FoamyGuy/3D-Printed-ESP8266-Remote/album_pics/2_part_design_assembled.png

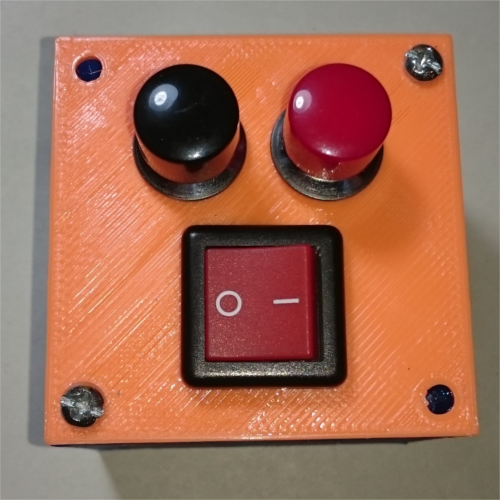
album_pics/2_part_design_assembled.png
