FoamyGuy/3D-Printed-ESP8266-Remote/album_pics/battery_brain_installed.png

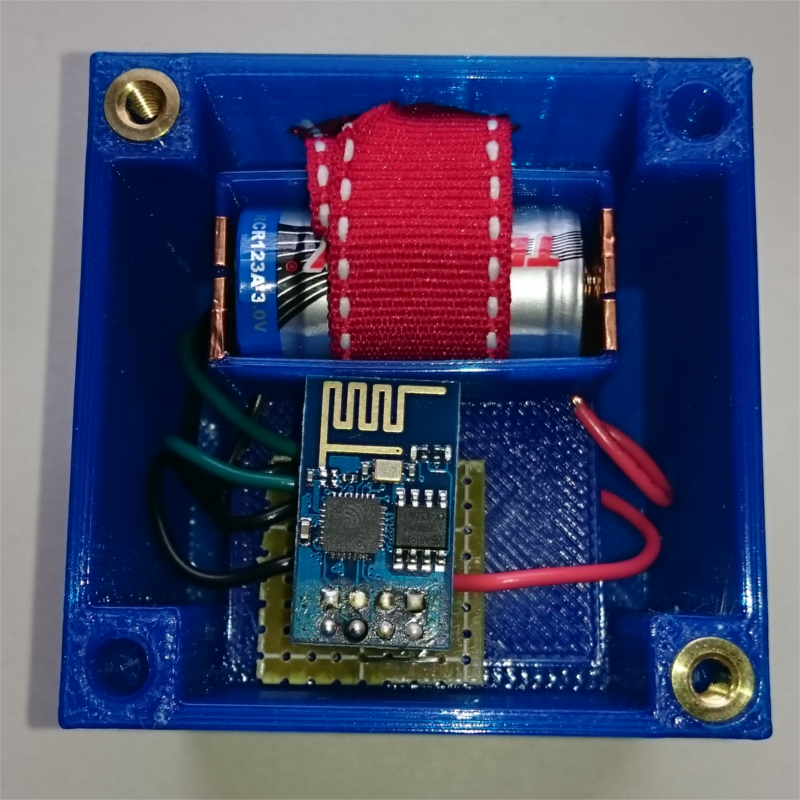
album_pics/battery_brain_installed.png
