FoamyGuy/3D-Printed-ESP8266-Remote/album_pics/buttons_switch_installed.png

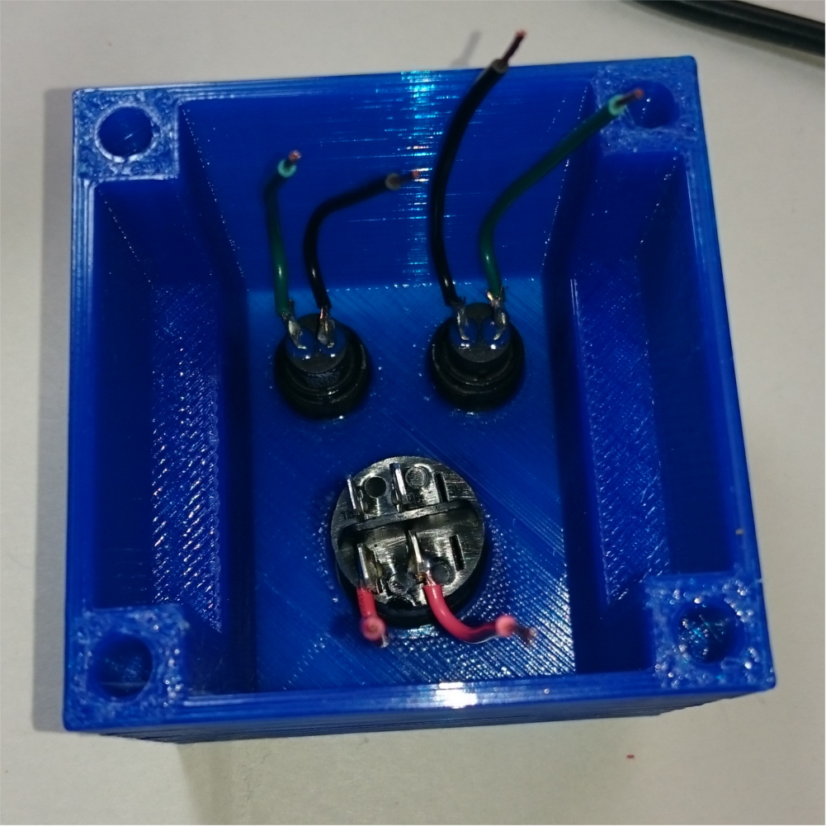
album_pics/buttons_switch_installed.png
